j-jovan/ESP8266_OTA/OTAWeb.ino

#include <WiFi.h>
#include <ESPmDNS.h>
#include <WiFiUdp.h>
#include <ArduinoOTA.h>

// Uredjaj se povezuje na Wi-Fi sa kredencijalima ispod
// Uredjaj je trebao da se ponasa kao ruter neko vreme i da
// iskljuci Wi-Fi ukoliko se klijent ne zakaci, ali to nismo jos resili

//const char* ssid = "polyhedralab";
//const char* password = "polyhedra3d";

const char* ssid = "Zmaj i Ala";
const char* password = "88888888";

void OTA_Setup() {

  Serial.println("Booting");
  WiFi_Off();
  WiFi.begin(ssid, password);
  //while (WiFi.waitForConnectResult() != WL_CONNECTED) {
  //Serial.println("Connection Failed! Rebooting...");
  //delay(5000);
  //ESP.restart();
  //}

  // Port defaults to 3232
  // ArduinoOTA.setPort(3232);

  // Hostname defaults to esp3232-[MAC]
  // ArduinoOTA.setHostname("myesp32");

  // No authentication by default
  // ArduinoOTA.setPassword("admin");

  // Password can be set with it's md5 value as well
  // MD5(admin) = 21232f297a57a5a743894a0e4a801fc3
  // ArduinoOTA.setPasswordHash("21232f297a57a5a743894a0e4a801fc3");

  ArduinoOTA
  .onStart([]() {
    String type;
    if (ArduinoOTA.getCommand() == U_FLASH)
      type = "sketch";
    else // U_SPIFFS
      type = "filesystem";

    // NOTE: if updating SPIFFS this would be the place to unmount SPIFFS using SPIFFS.end()
    Serial.println("Start updating " + type);
  })
  .onEnd([]() {
    Serial.println("\nEnd");
  })
  .onProgress([](unsigned int progress, unsigned int total) {
    Serial.printf("Progress: %u%%\r", (progress / (total / 100)));
  })
  .onError([](ota_error_t error) {
    Serial.printf("Error[%u]: ", error);
    if (error == OTA_AUTH_ERROR) Serial.println("Auth Failed");
    else if (error == OTA_BEGIN_ERROR) Serial.println("Begin Failed");
    else if (error == OTA_CONNECT_ERROR) Serial.println("Connect Failed");
    else if (error == OTA_RECEIVE_ERROR) Serial.println("Receive Failed");
    else if (error == OTA_END_ERROR) Serial.println("End Failed");
  });

  ArduinoOTA.begin();

  Serial.println("Ready");
  Serial.print("IP address: ");
  Serial.println(WiFi.localIP());
}

void OTAHandleClient()
{
  ArduinoOTA.handle();
}
bool WiFi_Off() {
  WiFi.disconnect();
  WiFi.mode(WIFI_OFF);
  //WiFi.forceSleepBegin();
}
